dylan7474/SleepRadioPi-OS/hardware/case/stl/tabs.stl

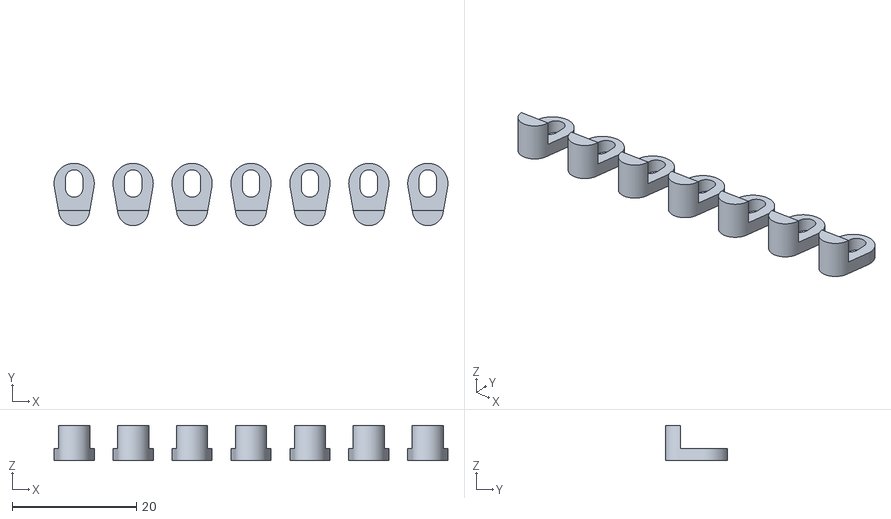
[picture p20: CAD file, 2026-09-29]
hardware/case/stl/tabs.stl
63.5 x 10.0 x 5.70
