dylan7474/SleepRadioPi-OS/hardware/case/stl/top_test.stl

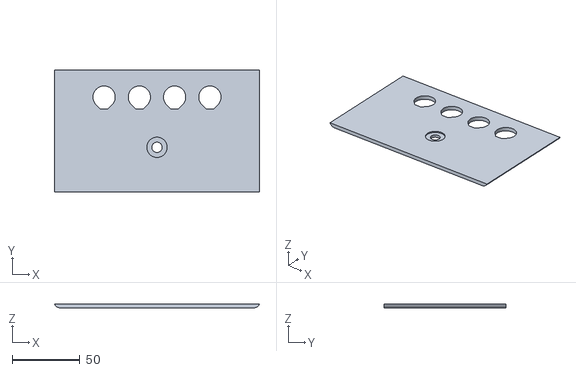
[picture p21: CAD file, 2026-09-29]
hardware/case/stl/top_test.stl
151.2 x 90.0 x 3.01
