dylan7474/SleepRadioPi-OS/hardware/case/stl/tube_buttons.stl

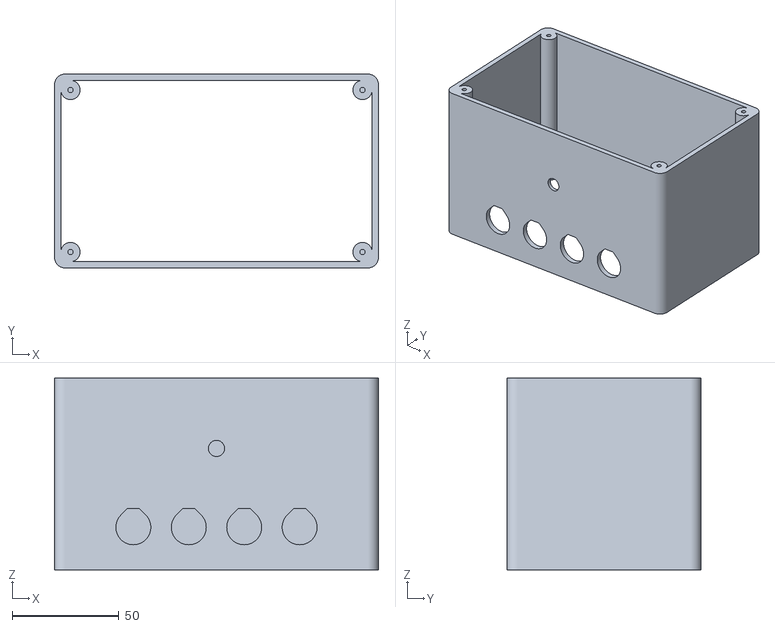
[picture p22: CAD file, 2026-09-29]
hardware/case/stl/tube_buttons.stl
152.0 x 91.0 x 90.0
