dylan7474/SleepRadioPi-OS/hardware/case/stl/strap_loops.stl

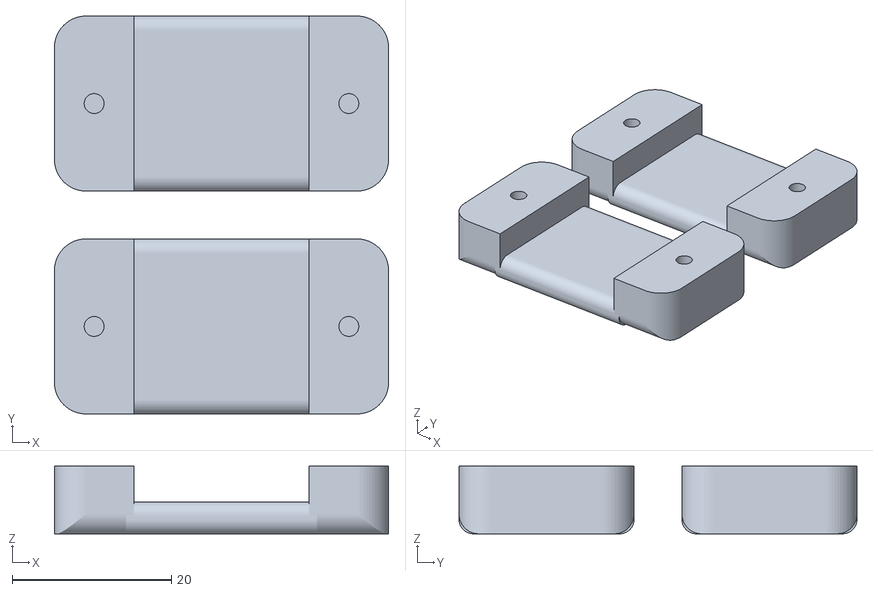
[picture p23: CAD file, 2026-09-27]
hardware/case/stl/strap_loops.stl
42.0 x 50.0 x 8.50
