dylan7474/SleepRadioPi-OS/hardware/case/stl/strap_guide.stl

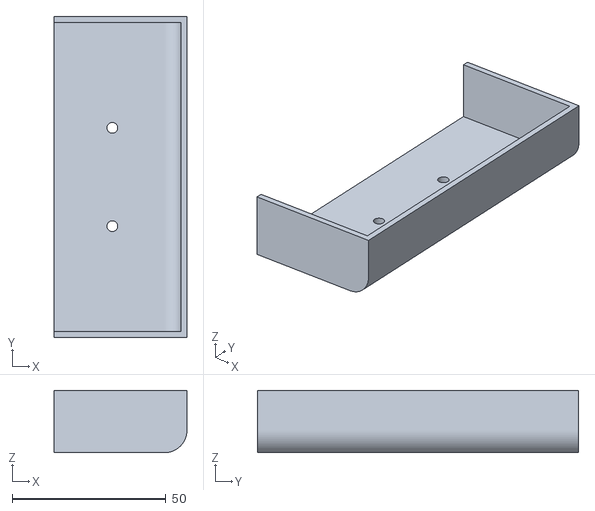
[picture p24: CAD file, 2026-09-27]
hardware/case/stl/strap_guide.stl
43.3 x 104.6 x 20.3
