dylan7474/SleepRadioPi-OS/hardware/case/stl/tube_handle.stl

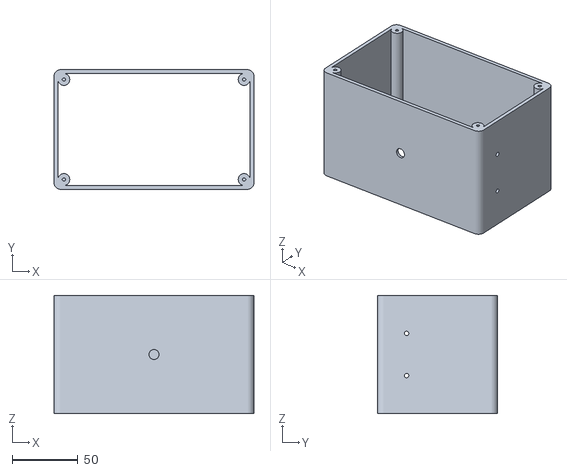
[picture p25: CAD file, 2026-09-27]
hardware/case/stl/tube_handle.stl
152.0 x 91.0 x 90.0
