dylan7474/SleepRadioPi-OS/hardware/case/stl/grommet.stl

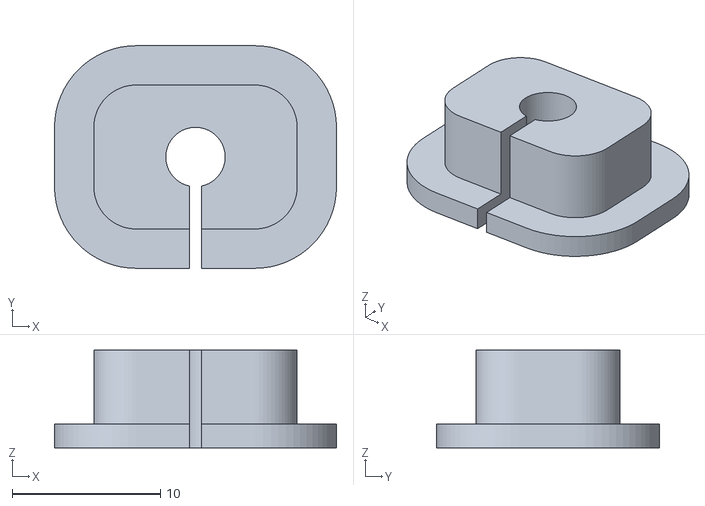
[picture p26: CAD file, 2026-09-27]
hardware/case/stl/grommet.stl
19.0 x 15.0 x 6.60
