dylan7474/SleepRadioPi-OS/hardware/case/stl/tube_ring.stl

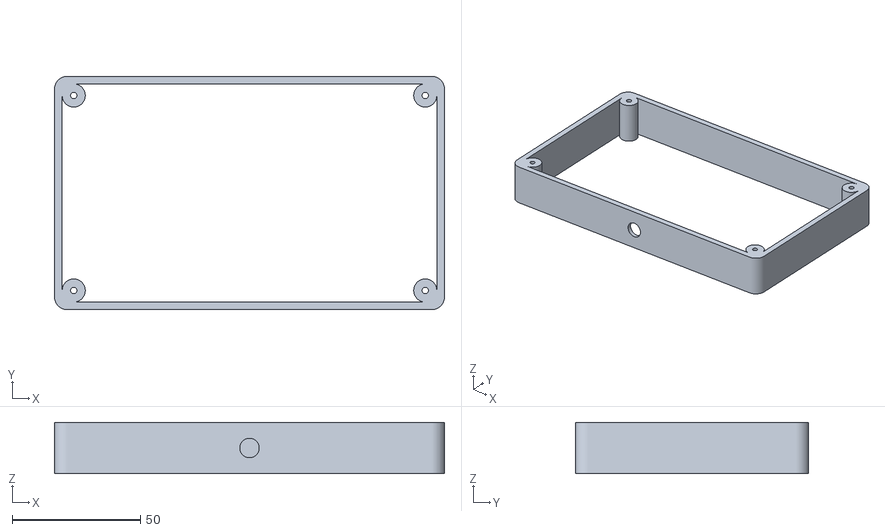
[picture p27: CAD file, 2026-09-26]
hardware/case/stl/tube_ring.stl
152.0 x 91.0 x 20.0
