dylan7474/SleepRadioPi-OS/hardware/case/sleepradiopi_box.scad

// SleepRadioPi box: a 3D-printable stereo radio cabinet for two small round
// speakers (Gikfun EK1794, 40 mm, no screw holes), a Raspberry Pi Zero 2 W +
// HiFiBerry MiniAmp, a DS3231 RTC and an EC11 rotary encoder in the top.
// No display.
//
// Printed parts that screw together:
//   tube  - top, bottom and sides in one piece, open front and back
//   front - baffle with two grilles; each speaker drops into a locating collar
//           behind its grille and is held by hot glue or three clamp tabs
//   rear  - back panel; the Pi, amp and RTC mount on its inside face, so the
//           whole electronics tray comes out with the panel
//   knob  - for the encoder's 6 mm D-shaft
//   tabs  - speaker clamp tabs (6 + 1 spare)
//   tube_ring - a 20 mm slice of the tube (same section, corner bosses and
//           knob hole) to test the panels and encoder before the full tube
//   grommet - closes the power cable slot round the cable (for the bass port)
//   strap_loops - two loops for a leather carry strap, screwed to the sides
//           from inside; strap_guide - a drill guide that clips over the box
//           to put the loops' screw holes in a tube printed without them
//   top_test - just the top wall of a -D buttons=true tube (the button and
//           knob holes), printed flat in ~40 min, to try the buttons first
//
// Render a part:
//   openscad --backend=manifold -D 'part="tube"' -o tube.stl sleepradiopi_box.scad
// part = "tube" | "tube_ring" | "front" | "rear" | "knob" | "tabs" | "grommet" | "front_plate" |
//        "strap_loops" | "strap_guide" | "top_test" |
//        "front_plate_noknob" |
//        "assembly" | "exploded" | "rear_inside" | "front_inside" | "check" | "check_pull"
//
// Coordinate frame: x across the box (0 = centre, +x = right seen from the
// front), y front to back (y = 0 is the front face), z up (0 = underside).
// Everything is in millimetres.

part = "assembly";

// A script font for the lettering, in fonts/ (SIL Open Font Licence, fonts/OFL-Lobster.txt):
// logo_font = "Lobster", with logo_fit = "together" (the Roberts Radio front)
use <fonts/Lobster-Regular.ttf>

// Draft: thin, fast fit-test panels (1.2 mm plate, open grille holes, no
// countersinks). Only for the front/rear/draft_plate parts -- never the tube.
draft = false;

// Lettering engraved into the front face between the speakers. Engraved, not
// raised: the front prints face down, and raised letters would need the whole
// panel on supports. Try -D front_logo=true with part="front" / "front_plate".
front_logo    = false;
logo_lines    = ["SLEEP", "RADIO"];
logo_font     = "Liberation Sans:style=Bold";
logo_w        = 36;      // every line is stretched to this width
logo_gap      = 4;       // between lines
logo_depth    = 0.8;     // 4 layers at 0.2 mm
logo_fit      = "stretch"; // "stretch": every line to logo_w (block capitals); "together": the lines
                         // scaled as one so the widest is logo_w, keeping the letters' shape (a script)

/* ---------- Speakers (CHECK WITH CALIPERS) ---------- */
spk_d        = 40;      // rim diameter (measured: 40 mm)
spk_rim_t    = 2.7;     // thickness of the flat front rim/flange (measured 2026-09-29)
spk_depth    = 22;      // front of the rim to the back of the magnet (UNVERIFIED)
spk_grille_d = 34;      // grille opening, a bit less than the rim so the rim seals
spk_fit      = 0.6;     // collar clearance on the diameter
collar_t     = 1.6;
clamp        = true;    // screw bosses for the clamp tabs (hot glue works without)
clamp_angles = [90, 210, 330];
clamp_r      = spk_d / 2 + collar_t + 3.2;  // boss centre radius
clamp_boss_d = 6.5;
clamp_boss_h = 6;       // boss height above the panel's inside face (screw grip)
clamp_pilot  = 2.1;     // M2.5 self-tapping (the M2.5 x 6 screws from the Pi kit)
tab_t        = 2;

/* ---------- Pi Zero 2 W + MiniAmp (datasheet values, as in the old case) ---------- */
pcb_l      = 65;
pcb_w      = 30;
pcb_t      = 1.6;
hole_in    = 3.5;
port_otg_u = 41.4;       // port centres along the long edge, from the SD end
port_pwr_u = 54;
amp_gap    = 12;         // Pi to amp, on the header
term_u0    = 23.9;       // MiniAmp speaker terminal, along the port edge
term_u1    = 44.4;
term_h     = 10;

/* ---------- Box ---------- */
inner_w     = 146;
inner_h     = 85;
ring_len    = 20;        // "tube_ring": a short slice of the tube for a fit test
tube_len    = part == "tube_ring" ? ring_len : 90;  // inside depth, front panel to rear panel
wall        = 3;
panel_t     = draft ? 1.2 : 5;
grille_t    = draft ? panel_t : 2.4;  // grille thickness; the rest is a recess for the cone
spk_x       = 45;        // speaker centres at +-spk_x
corner_r    = 5;

boss_r      = 4.5;       // screw bosses in the tube corners, for the panels
boss_off    = 4.5;       // boss centre from the inner walls
pilot_d     = 2.5;       // M3 self-tapping screws into the bosses
pilot_len   = 16;
panel_screw_d = 3.4;
panel_csk_d   = 6.6;

lip_t       = 1.6;       // locating lip on each panel, fits inside the tube
lip_h       = 3;
lip_clr     = 0.3;

hex_flat    = 3.2;       // grille: hexagonal holes, flat to flat
hex_web     = 1.2;
grille_style = "hex";    // "hex" or "sunburst" (art deco: a fan rising from the bottom)
sun_rays    = 9;         // sunburst: rays from the half-sun at the bottom of the grille
sun_spread  = 80;        // ...fanned out to +-this many degrees from vertical
sun_hub_r   = 8;         // the half-sun
sun_arc_r   = 20;        // arc across the rays; above it an extra ray between each pair
sun_rib_w   = 1.6;       // rays and arc (4 perimeters at 0.4 mm)

/* ---------- Rear panel electronics ---------- */
pi_dx       = 0;         // Pi position: offset from the centre line
post_h      = 7;         // room under the Pi for header stubs + encoder wires
post_d      = 6;         // tip, under the Pi
post_d2     = 7.6;       // below the tip
// The Pi: four M2.5 self-tappers down through its corner holes into solid
// posts (the heads sit on the Pi). The back of the panel stays plain. The
// amp sits on the Pi's header; no standoffs.
pi_tap_d      = 2.2;     // pilot for an M2.5 self-tapper (prints ~2.0; tested)

cable_dx    = 32;        // power cable slot: this far out from the Pi's port edge
cable_w     = 14;
cable_h     = 10;

// Bass port (-D rear_port=true). The box is ~0.95 L inside (both speakers
// share it); a 20 mm port 22 mm long (the panel + a tube inside) tunes it to
// ~160 Hz, just below where 40 mm speakers give up. The cable slot is a vent
// too (~160 Hz on its own), so close it with the grommet when the port is on,
// and set the radio's low cut (speaker_highpass_hz) to ~140 Hz so the bass EQ
// doesn't push the speakers below the port's note.
rear_port   = false;
port_d      = 20;
port_len    = 22;        // outside face to the tube's inner end
port_wall   = 1.6;
port_flare  = 3;         // 45-degree flare at both ends: quieter, no supports needed
port_pos    = [47, 30];  // (x, z): low down on the side away from the RTC
box_net_l   = 0.95;      // inside volume less the speakers, Pi, bosses (estimated)

grommet_clr     = 0.15;  // plug vs the slot, each side
grommet_cable_d = 4;     // micro-USB cable (CHECK WITH CALIPERS)
grommet_slit    = 0.8;   // so it springs round the cable
grommet_flange  = 2.5;   // outside lip, all round
grommet_flange_t = 1.6;

rtc         = true;      // ZS-042 DS3231: a locating rim, fix with foam tape
rtc_w       = 22.5;
rtc_l       = 38.5;
rtc_gap     = 17;        // from the Pi's GPIO edge to the RTC rim

/* ---------- Encoder + knob ---------- */
enc_hole_d  = 7.6;       // EC11 M7 bushing (a little over, for the sideways print)
enc_teardrop = false;    // true = pointed top, for printers that sag on round holes
enc_pocket_d = 15;       // thin the top wall around it so the nut gets thread
enc_pocket  = 1;
knob_d      = 30;
knob_h      = 20;
knob_style  = "plain";   // "plain" (pointer groove) or "sunburst" (the grille's fan
                         // engraved in the top; it rises towards where the groove points)
knob_sun_d  = 26;
knob_sun_rays = 7;
knob_sun_rib_w = 1.4;
knob_engrave = 0.8;
shaft_d     = 6.15;
shaft_flat  = 4.65;
shaft_len   = 16.5;      // bore depth: a 20 mm EC11 shaft stands ~18 mm above the
                         // case (2 mm wall at the pocket), so the knob clears it by ~1.5 mm
nut_recess_d = 12;       // under the knob, round the encoder's M7 nut + washer
nut_recess_h = 3;

/* ---------- Preset buttons ---------- */
// Four chunky momentary panel buttons (16 mm stainless, screw terminals) in a
// row across the top, near the front, with the knob on its own further back:
// the channels and the volume in separate places, which is easier to follow
// (the radio is for an elderly listener). Wiring: hardware/wiring.
// -D buttons=true puts the holes in the tube and moves the knob back
// btn_knob_back mm to make room; part="top_test" is just that top, to try
// the buttons before printing a whole tube.
buttons     = false;
btn_hole_d  = 16.4;      // 16 mm thread (CHECK the buttons)
btn_x       = [-39, -13, 13, 39];   // 26 mm apart; the outer two miss the speakers' top
                                    // clamp tabs (and screws) at +-45
btn_y       = 25;        // from the front face: clear of the front panel's lip and the
                         // clamp tabs, and ~13 mm in front of the knob
btn_knob_back = 12;      // the knob moves this far back with the buttons in
btn_teardrop = true;     // the holes print sideways (the tube stands on its front end): a
                         // teardrop top, cut flat just inside the button's head, so there's
                         // no overhang to curl up and catch the nozzle (and it's hidden)
btn_head_d  = 19;        // the flat head above the top (CHECK)
btn_head_h  = 3;
btn_nut_d   = 22;        // the nut inside, across its corners (CHECK)
btn_body_d  = 18;        // below the nut: the switch body and its screw terminals (CHECK)
btn_body_h  = 30;        // top of the wall to the ends of the terminals (CHECK)

/* ---------- Carry strap ---------- */
// A leather strap over the top, through a loop on each side: the strap goes
// down behind the loop's bar, folds back up over it and is fixed to itself
// above the loop (Chicago screws or rivets). Each loop has two M3 x 10
// self-tappers from inside the box, through the side wall into its pilots.
// -D handle=true puts the holes in the tube; for a tube printed without them,
// drill them through strap_guide.
handle      = false;
strap_w     = 20;        // leather strap (CHECK: the channel is 2 mm wider)
strap_t     = 4;         // ...and its thickness (the channel is 0.5 mm deeper)
loop_side   = 10;        // screw lugs either side of the strap channel
loop_h      = 22;        // top to bottom
loop_bar    = 4;         // the bar the strap folds round
loop_top    = 11;        // below the top of the box (clear of the corner bosses inside)
loop_pilot  = 2.5;       // M3 self-tapping
loop_skin   = 1.2;       // plastic left over the end of each pilot
loop_hole_d = 3.4;       // through the side wall
guide_hole_d = 3.5;      // the drill guide's holes: drill 3.5 mm
guide_t     = 2;
guide_clr   = 0.3;

$fn = 64;

/* ---------- Derived ---------- */
W  = inner_w + 2 * wall;
H  = inner_h + 2 * wall;
D  = tube_len + 2 * panel_t;
ti = panel_t;                 // tube front end (inside face of the front panel)
to = panel_t + tube_len;      // tube rear end (inside face of the rear panel)

spk_z   = H / 2;
spk_pos = [[-spk_x, spk_z], [spk_x, spk_z]];
collar_h = spk_rim_t - 0.4;   // a little under the rim, so the tabs clamp the speaker
function clamp_pts(p) = [for (a = clamp_angles) p + clamp_r * [cos(a), sin(a)]];

bx = inner_w / 2 - boss_off;
bz0 = wall + boss_off;
bz1 = H - wall - boss_off;
bosses = [[-bx, bz0, -1, -1], [bx, bz0, 1, -1], [-bx, bz1, -1, 1], [bx, bz1, 1, 1]];

enc_y = ti + tube_len / 2 + (buttons ? btn_knob_back : 0);

loop_cw = strap_w + 2;                       // strap channel width
loop_gap = strap_t + 0.5;                    // channel depth (the strap runs between the wall and the bar)
loop_t = loop_gap + loop_bar;                // how far a loop stands out from the side
loop_l = loop_cw + 2 * loop_side;
loop_dy = loop_cw / 2 + loop_side / 2;       // screws either side of the middle
loop_y = D / 2;                              // centred front to back (the balance point)
loop_z = H - loop_top - loop_h / 2;
loop_screws = [for (sx = [-1, 1]) for (dy = [-loop_dy, loop_dy]) [sx, loop_y + dy]];

// Pi on the rear panel, long side vertical, SD end down, parts facing forward,
// ports on the +x edge.
pi_x0   = pi_dx - pcb_w / 2;
pi_z0   = H / 2 - pcb_l / 2;
pi_y    = to - post_h;               // Pi underside
pi_top  = pi_y - pcb_t;              // component side (faces the front)
amp_y   = pi_top - amp_gap;          // amp underside
amp_top = amp_y - pcb_t;
port_x  = pi_x0 + pcb_w;             // port edge
function pi_pt(u, v) = [port_x - v, pi_z0 + u];  // board coords -> (x, z)
pi_holes = [for (u = [hole_in, pcb_l - hole_in]) for (v = [hole_in, pcb_w - hole_in]) pi_pt(u, v)];
cable_pos = [port_x + cable_dx, pi_z0 + port_pwr_u];
rtc_pos   = [pi_x0 - rtc_gap - rtc_w / 2, H / 2];

if (rear_port) {
    a = PI * port_d * port_d / 4;
    leff = port_len + 0.85 * port_d;   // end correction 1.7 r
    echo(str("Bass port: ", port_d, " mm x ", port_len, " mm -> tuned to about ",
             round(343000 / (2 * PI) * sqrt(a / (box_net_l * 1e6 * leff))), " Hz"));
}

echo(str("Outer size: ", W, " x ", D, " x ", H, " mm (w x d x h); inside ",
         inner_w, " x ", tube_len, " x ", inner_h, " = ",
         round(inner_w * tube_len * inner_h / 1e4) / 100, " L"));

// The speaker mounts must stay clear of the lip and the corner bosses.
lip_in = [inner_w / 2 - lip_clr - lip_t, inner_h / 2 - lip_clr - lip_t];
for (p = spk_pos) for (c = concat([p + [sign(p[0]) * (spk_d / 2 + collar_t), 0]],
                                  clamp ? clamp_pts(p) : [])) {
    r = norm(c - p) > spk_d / 2 + collar_t + 0.1 ? clamp_boss_d / 2 : 0;
    assert(abs(c[0]) + r < lip_in[0] - 0.5 && abs(c[1] - H / 2) + r < lip_in[1] - 0.5,
           "A speaker mount hits the panel lip: move spk_x or the clamp angles");
    for (b = bosses) assert(norm(c - [b[0], b[1]]) > r + boss_r + 1, "A speaker mount hits a corner boss");
}

/* ---------- Helpers ---------- */
module rrect(x0, z0, x1, z1, r) {
    r = max(r, 0.01);
    hull() for (x = [x0 + r, x1 - r], z = [z0 + r, z1 - r]) translate([x, z]) circle(r = r);
}
// Extrude an (x, z) profile along y from y0 to y1.
module yext(y0, y1) translate([0, y1, 0]) rotate([90, 0, 0]) linear_extrude(y1 - y0) children();
// A cylinder along y.
module ycyl(x, z, y0, y1, d, d2 = undef)
    translate([x, y0, z]) rotate([-90, 0, 0]) cylinder(d1 = d, d2 = is_undef(d2) ? d : d2, h = y1 - y0);

module outer2d() rrect(-W / 2, 0, W / 2, H, corner_r);
module inner2d(inset = 0)
    rrect(-inner_w / 2 + inset, wall + inset, inner_w / 2 - inset, H - wall - inset,
          max(corner_r - wall - inset, 0.5));

// Corner boss profile: a circle hulled into the corner.
module boss2d(b, grow = 0) hull() {
    translate([b[0], b[1]]) circle(r = boss_r + grow);
    translate([b[0] + b[2] * (boss_off + grow), b[1] + b[3] * (boss_off + grow)]) square(0.02, center = true);
    translate([b[0] + b[2] * (boss_off + grow), b[1] - b[3] * grow]) square(0.02, center = true);
    translate([b[0] - b[2] * grow, b[1] + b[3] * (boss_off + grow)]) square(0.02, center = true);
}

/* ---------- Tube ---------- */
module teardrop2d(d) hull() {   // point towards +y (up while the tube prints)
    circle(d = d);
    translate([0, d / 2 * sqrt(2)]) square(0.02, center = true);
}

module enc2d(d) if (enc_teardrop) teardrop2d(d); else circle(d = d);
module btn2d(d) if (btn_teardrop) intersection() {
    teardrop2d(d);
    translate([-d, -d]) square([2 * d, d + min(d / 2 * sqrt(2), btn_head_d / 2 - 0.75)]);
} else circle(d = d);

module tube() {
    difference() {
        union() {
            yext(ti, to) difference() { outer2d(); inner2d(); }
            for (b = bosses) yext(ti, to) boss2d(b);
        }
        for (b = bosses) {
            ycyl(b[0], b[1], ti - 1, ti + pilot_len, pilot_d);
            ycyl(b[0], b[1], to - pilot_len, to + 1, pilot_d);
        }
        if (handle) strap_holes(loop_hole_d);
        if (buttons) for (x = btn_x)
            translate([x, btn_y, H - wall - 1]) linear_extrude(wall + 2) btn2d(btn_hole_d);
        // Encoder hole in the top, with a thinner patch of wall around it.
        translate([0, enc_y, H - wall - 1]) linear_extrude(wall + 2) enc2d(enc_hole_d);
        translate([0, enc_y, H - wall - 1]) linear_extrude(1 + enc_pocket) enc2d(enc_pocket_d);
    }
}

/* ---------- Panels (shared) ---------- */
// Built with the outside face at y = 0 and the inside face at y = panel_t,
// the lip sticking out to y = panel_t + lip_h.
module panel_blank() {
    yext(0, panel_t) outer2d();
    yext(panel_t - 0.01, panel_t + lip_h) difference() {
        inner2d(lip_clr);
        inner2d(lip_clr + lip_t);
        for (b = bosses) boss2d(b, 0.6);
    }
}
module panel_screw_holes() for (b = bosses) {
    ycyl(b[0], b[1], -1, panel_t + 1, panel_screw_d);
    if (!draft) ycyl(b[0], b[1], -0.01, (panel_csk_d - panel_screw_d) / 2, panel_csk_d, panel_screw_d);
}

/* ---------- Front panel ---------- */
hex_pitch = hex_flat + hex_web;
module grille2d(style = grille_style) {
    if (style == "sunburst") sunburst2d(); else hex2d();
}
// Art deco sunburst, 1930s radio style: rays fan up from a half-sun at the
// bottom of the grille, with an arc across them and extra rays above the arc
// so the top slots stay narrow. The open slots are what's left of the circle.
// d and rays default to the speaker grille; the hub and arc scale with d.
module sunburst2d(d = spk_grille_d, rays = sun_rays, rib_w = sun_rib_w) {
    k = d / spk_grille_d;
    step = 2 * sun_spread / (rays - 1);
    module ray(a, r0) rotate(90 + a) translate([r0, -rib_w / 2]) square([d * 2, rib_w]);
    translate([0, -d / 2]) difference() {
        translate([0, d / 2]) circle(d = d);
        circle(r = sun_hub_r * k);
        for (i = [0 : rays - 1]) ray(-sun_spread + i * step, 0);
        for (i = [0 : rays - 2]) ray(-sun_spread + (i + 0.5) * step, sun_arc_r * k);
        difference() { circle(r = sun_arc_r * k + rib_w / 2); circle(r = sun_arc_r * k - rib_w / 2); }
    }
}
module hex2d() intersection() {
    circle(d = spk_grille_d);
    n = ceil(spk_grille_d / hex_pitch);
    for (j = [-n : n]) for (i = [-n : n])
        translate([(i + (j % 2) / 2) * hex_pitch, j * hex_pitch * sqrt(3) / 2])
            rotate(30) circle(d = hex_flat / cos(30), $fn = 6);
}

module front(logo = front_logo, grille = grille_style) {
    difference() {
        union() {
            panel_blank();
            for (p = spk_pos) translate([p[0], 0, p[1]]) {
                // Locating collar around the speaker rim
                yext(panel_t - 0.01, panel_t + collar_h) difference() {
                    circle(d = spk_d + spk_fit + 2 * collar_t);
                    circle(d = spk_d + spk_fit);
                }
            }
            if (clamp) for (p = spk_pos) for (c = clamp_pts(p))
                ycyl(c[0], c[1], panel_t - 0.01, panel_t + clamp_boss_h, clamp_boss_d);
        }
        panel_screw_holes();
        for (p = spk_pos) translate([p[0], 0, p[1]]) {
            yext(-1, panel_t + 1) if (draft) circle(d = spk_grille_d); else grille2d(grille);
            yext(grille_t, panel_t + 1) circle(d = spk_grille_d);  // cone clearance
        }
        if (clamp) for (p = spk_pos) for (c = clamp_pts(p))
            ycyl(c[0], c[1], draft ? -1 : 1.2, panel_t + clamp_boss_h + 1, clamp_pilot);
        if (logo && !draft) yext(-1, logo_depth) logo2d();
    }
}


// The lettering, centred between the speakers: each line the same width, or (logo_fit
// "together") all scaled as one, keeping the font's shape
module logo2d() {
    if (logo_fit == "together") logo_together2d(); else logo_stretched2d();
}
module logo_together2d() {
    n = len(logo_lines);
    translate([0, spk_z]) resize([logo_w, 0], auto = true)
        for (i = [0 : n - 1])
            translate([0, ((n - 1) / 2 - i) * 13])
                text(logo_lines[i], size = 10, font = logo_font, halign = "center", valign = "center");
}
module logo_stretched2d() {
    n = len(logo_lines);
    line_h = logo_line_h();
    total = n * line_h + (n - 1) * logo_gap;
    for (i = [0 : n - 1])
        translate([0, spk_z + total / 2 - line_h / 2 - i * (line_h + logo_gap)])
            resize([logo_w, line_h])
                text(logo_lines[i], size = 10, font = logo_font, halign = "center", valign = "center");
}
// Cap height once a line is stretched to logo_w (Liberation Sans Bold caps
// are about 0.72 x size tall and ~0.72 x size wide per letter)
function logo_line_h() = logo_w / max([for (l = logo_lines) len(l)]) * 1.0;

/* ---------- Speaker clamp tab ---------- */
// Stepped tab: the plate sits on the tall boss with the screw in the slot, and
// a foot under the rounded nose reaches down and presses on the rim. The foot
// stops short of the boss, even with the tab pulled back along its slot.
// Local z = 0 is the foot's underside; the plate is on top.
tab_len  = clamp_r - spk_d / 2 + 2;    // reaches 2 mm over the rim
tab_drop = clamp_boss_h - collar_h;    // foot height: rim + 0.4 mm press
tab_foot_x = -(clamp_boss_d / 2 + 0.8 + 0.3);
module tab2d() difference() {
    hull() { circle(d = clamp_boss_d); translate([-tab_len + 2.5, 0]) circle(d = 5); }
    hull() for (dx = [-0.8, 0.8]) translate([dx, 0]) circle(d = 2.8);  // slot for the M2.5 screw
}
module tab() {
    translate([0, 0, tab_drop]) linear_extrude(tab_t) tab2d();
    linear_extrude(tab_drop + 0.01) intersection() {
        tab2d();
        translate([tab_foot_x - 20, -10]) square([20, 20]);
    }
}
module tab_print() translate([0, 0, tab_drop + tab_t]) mirror([0, 0, 1]) tab();  // plate down, foot up

/* ---------- Rear panel ---------- */
// Built in place (outside face at y = D), so the Pi coordinates line up.
module rear() {
    difference() {
        union() {
            translate([0, D, 0]) mirror([0, 1, 0]) panel_blank();
            // Solid posts: a narrow tip next to the board (clear of the header
            // pins), thicker below.
            for (h = pi_holes) {
                ycyl(h[0], h[1], pi_y, pi_y + 3, post_d);
                ycyl(h[0], h[1], pi_y + 3 - 0.01, to + 0.01, post_d2);
            }
            if (rtc) yext(to - 3, to + 0.01) translate(rtc_pos) difference() {
                square([rtc_w + 2.4, rtc_l + 2.4], center = true);
                square([rtc_w, rtc_l], center = true);
                square([rtc_w - 6, rtc_l + 4], center = true);  // gaps for the header wires
            }
            if (rear_port) port_tube();
        }
        if (rear_port) port_bore();
        translate([0, D, 0]) mirror([0, 1, 0]) panel_screw_holes();
        // Self-tapper pilots, stopping 1.2 mm short of the outside face
        for (h = pi_holes) ycyl(h[0], h[1], pi_y - 1, D - 1.2, pi_tap_d);
        // Power cable slot (the micro-USB plug threads through it) + zip-tie slots
        yext(to - 1, D + 1) {
            translate(cable_pos) rrect(-cable_w / 2, -cable_h / 2, cable_w / 2, cable_h / 2, 3);
            for (dz = [-8, 8]) translate(cable_pos + [cable_w / 2 + 6, dz])
                square([5, 3], center = true);
        }
    }
}

// Bass port: a tube on the inside face, flared at both ends.
port_tip = D - port_len;                 // y of the tube's inner end
module port_tube() {
    od = port_d + 2 * port_wall;
    ycyl(port_pos[0], port_pos[1], port_tip + port_flare, to + 0.01, od);
    ycyl(port_pos[0], port_pos[1], port_tip, port_tip + port_flare + 0.01, od + 2 * port_flare, od);
}
module port_bore() {
    ycyl(port_pos[0], port_pos[1], port_tip - 1, D + 1, port_d);
    ycyl(port_pos[0], port_pos[1], port_tip - 0.01, port_tip + port_flare, port_d + 2 * port_flare, port_d);
    ycyl(port_pos[0], port_pos[1], D - port_flare, D + 0.01, port_d, port_d + 2 * port_flare);
}

/* ---------- Grommet (print flange down) ---------- */
// Fills the power cable slot round the cable once the plug is through. Open
// the slit, clip it round the cable, press it into the slot from outside.
module grommet() {
    module slot2d(grow) rrect(-cable_w / 2 - grow, -cable_h / 2 - grow,
                              cable_w / 2 + grow, cable_h / 2 + grow, 3 + max(grow, -2.9));
    difference() {
        union() {
            linear_extrude(grommet_flange_t) slot2d(grommet_flange);
            linear_extrude(grommet_flange_t + panel_t) slot2d(-grommet_clr);
        }
        translate([0, 0, -1]) {
            cylinder(d = grommet_cable_d, h = panel_t + grommet_flange_t + 2);
            translate([-grommet_slit / 2, -cable_h, 0]) cube([grommet_slit, cable_h, panel_t + grommet_flange_t + 2]);
        }
    }
}
module grommet_in_place() translate([cable_pos[0], D + grommet_flange_t, cable_pos[1]])
    rotate([90, 0, 0]) grommet();

/* ---------- Knob (print top face down) ---------- */
/* ---------- Carry strap loops ---------- */
// Extrude a (y, z) profile along x from x0 to x1.
module xext(x0, x1) translate([x0, 0, 0]) rotate([90, 0, 90]) linear_extrude(x1 - x0) children();

// One loop, built with x along the strap's width, y up and z out from the
// side wall (z = 0 against the wall).
module strap_loop() {
    difference() {
        intersection() {
            translate([0, 0, -1]) linear_extrude(loop_t + 2)
                rrect(-loop_l / 2, -loop_h / 2, loop_l / 2, loop_h / 2, 4);
            union() {
                // the screw lugs: rounded on the outside
                for (sx = [-1, 1]) xext(sx > 0 ? loop_cw / 2 : -loop_l / 2 - 1,
                                        sx > 0 ? loop_l / 2 + 1 : -loop_cw / 2) hull() {
                    translate([-loop_h / 2, 0]) square([loop_h, 0.01]);
                    for (y = [-1, 1]) translate([y * (loop_h / 2 - 2.5), loop_t - 2.5]) circle(r = 2.5);
                }
                // the bar, rounded all round so the leather folds over it easily
                xext(-loop_cw / 2 - 1, loop_cw / 2 + 1) rrect(-loop_h / 2, loop_gap, loop_h / 2, loop_t, 1.8);
            }
        }
        for (sx = [-1, 1]) translate([sx * loop_dy, 0, -1]) cylinder(d = loop_pilot, h = 1 + loop_t - loop_skin);
    }
}
// The loops on the box: the right one, and the left one mirrored.
module strap_loops_placed() for (sx = [-1, 1]) mirror([sx < 0 ? 1 : 0, 0, 0])
    multmatrix([[0, 0, 1, W / 2], [1, 0, 0, loop_y], [0, 1, 0, loop_z], [0, 0, 0, 1]]) strap_loop();
// The screw holes through the side walls (also the screws, for the checks).
module strap_holes(d, len = wall + 2) for (sc = loop_screws)
    translate([sc[0] * (W / 2 - wall - 1 + len / 2), sc[1], loop_z]) rotate([0, 90, 0]) cylinder(d = d, h = len, center = true);
// M3 x 10: a pan head inside the box, 3 mm of wall, 7 mm into the loop.
module strap_screws() {
    strap_holes(3, 10 + 2);
    for (sc = loop_screws) translate([sc[0] * (W / 2 - wall - 1.2), sc[1], loop_z]) rotate([0, 90, 0])
        cylinder(d = 5.6, h = 2.4, center = true);
}
// Drill guide for a tube without the holes: clips over the top corner of the
// assembled box, between stops on the front and back panels' faces, and
// turns round end to end for the other side. Drill 3.5 mm through its holes.
module strap_guide() {
    win = [W / 2 - 18, loop_z - loop_h / 2 - 8];
    module window() translate(win) square([40, 60]);
    difference() {
        union() {
            yext(-guide_clr, D + guide_clr) intersection() {
                difference() { offset(r = guide_clr + guide_t) outer2d(); offset(r = guide_clr) outer2d(); }
                window();
            }
            for (y = [-guide_clr - guide_t, D + guide_clr]) yext(y, y + guide_t)
                intersection() { offset(r = guide_clr + guide_t) outer2d(); window(); }
        }
        for (sc = loop_screws) if (sc[0] > 0)
            translate([W / 2 - 1, sc[1], loop_z]) rotate([0, 90, 0]) cylinder(d = guide_hole_d, h = 10);
    }
}

// Just the top wall of the tube (with the buttons' and the knob's holes),
// printed flat, outside face down: try the buttons, nuts and spacing first.
module top_test() intersection() {
    tube();
    translate([-W / 2 - 1, ti, H - wall - 0.01]) cube([W + 2, tube_len, wall + 1]);
}

module knob(style = knob_style) {
    difference() {
        union() {
            cylinder(d = knob_d - 1.2, h = knob_h);
            for (a = [0 : 360 / 36 : 359]) rotate([0, 0, a])
                translate([knob_d / 2 - 1.1, 0, 0]) cylinder(d = 1.8, h = knob_h, $fn = 12);
        }
        translate([0, 0, -0.01]) intersection() {
            cylinder(d = shaft_d, h = shaft_len);
            translate([-shaft_d / 2, -shaft_d / 2, 0]) cube([shaft_flat, shaft_d, shaft_len]);
        }
        translate([0, 0, -0.01]) cylinder(d = nut_recess_d, h = nut_recess_h);
        // Hollow skirt around the shaft so the knob clears the nut
        translate([0, 0, -0.01]) difference() {
            cylinder(d = knob_d - 6, h = 4);
            cylinder(d = shaft_d + 4, h = 4);
        }
        if (style == "sunburst")
            translate([0, 0, knob_h - knob_engrave]) linear_extrude(knob_engrave + 0.01)
                rotate(-90) sunburst2d(knob_sun_d, knob_sun_rays, knob_sun_rib_w);
        else
            translate([0, -0.7, knob_h - 1]) cube([knob_d / 2 - 3, 1.4, 1.2]);
    }
}

/* ---------- Part models for previews and checks ---------- */
module speaker_model(p) color("dimgray") translate([p[0], 0, p[1]]) {
    ycyl(0, 0, ti, ti + spk_rim_t, spk_d);
    ycyl(0, 0, ti + spk_rim_t, ti + spk_depth - 8, spk_d - 6, 20);   // basket
    ycyl(0, 0, ti + spk_depth - 8, ti + spk_depth, 24);
    // Solder tabs, placed between two clamp bosses
    rotate([0, -30, 0]) translate([spk_d / 2 - 5, ti + spk_rim_t + 1, -2]) cube([6, 4, 4]);
}
module tabs_in_place() color("orange") for (p = spk_pos) for (a = clamp_angles)
    translate([p[0], 0, p[1]]) rotate([0, -a, 0]) translate([clamp_r, ti + spk_rim_t, 0])
        rotate([-90, 0, 0]) tab();

module pi_stack_model() {
    module board(y, c) color(c) yext(y - pcb_t, y) translate([pi_x0, pi_z0]) square([pcb_w, pcb_l]);
    board(pi_y, "green");
    board(amp_y, "darkgreen");
    // GPIO header + socket along the far edge
    color("black") yext(amp_y, pi_top) translate([pi_x0 + 0.5, pi_z0 + 7]) square([5, 51]);
    color("black") yext(pi_y, pi_y + 3) translate([pi_x0 + 0.5, pi_z0 + 7]) square([5, 51]);  // pin stubs
    // Ports
    color("silver") for (u = [port_otg_u, port_pwr_u])
        yext(pi_top - 2.6, pi_top) translate([port_x - 5, pi_z0 + u - 4]) square([5.5, 8]);
    // Amp speaker terminal
    color("dimgray") yext(amp_top - term_h, amp_top)
        translate([port_x - 7.5, pi_z0 + term_u0]) square([7.9, term_u1 - term_u0]);
    // Micro-USB power plug + cable bend: keep-out volume
    color("white", 0.8) yext(pi_top - 8, pi_top + 1)
        translate([port_x - 0.5, pi_z0 + port_pwr_u - 5.5]) square([24, 11]);
    // RTC module (board + CR2032 holder behind it)
    if (rtc) color("steelblue") yext(to - 9, to)
        translate(rtc_pos) square([rtc_w - 0.4, rtc_l - 0.4], center = true);
}

module encoder_model() color("gray") translate([0, enc_y, 0]) {
    translate([-6.5, -6.5, H - wall - 7]) cube([13, 13, 7]);
    translate([-5, -4, H - wall - 12]) cube([10, 8, 5]);   // pins + wires
    translate([0, 0, H - wall - 7]) cylinder(d = 6, h = wall + 7 + 14);
    translate([0, 0, H - wall]) cylinder(d = 7, h = wall + 5);
}

module knob_in_place() color("orange") translate([0, enc_y, H + 2]) knob();

// The preset buttons, fitted: cap above the top, thread through it, nut and body below.
module buttons_model() color("goldenrod") for (x = btn_x) translate([x, btn_y, 0]) {
    translate([0, 0, H]) cylinder(d = btn_head_d, h = btn_head_h);
    translate([0, 0, H - wall]) cylinder(d = 11.9, h = wall);
    translate([0, 0, H - wall - 2]) cylinder(d = btn_nut_d, h = 2, $fn = 6);   // (d = across the corners)
    translate([0, 0, H - btn_body_h]) cylinder(d = btn_body_d, h = btn_body_h - wall - 2);
}

// Uncoloured versions for mockup.scad (it picks its own colours)
module knob_placed(style = knob_style) translate([0, enc_y, H + 2]) knob(style);
module speakers_placed() for (p = spk_pos) translate([p[0], 0, p[1]]) {
    ycyl(0, 0, ti, ti + spk_rim_t, spk_d);
    ycyl(0, 0, ti + spk_rim_t, ti + spk_depth - 8, spk_d - 6, 20);
}

module models() {
    for (p = spk_pos) speaker_model(p);
    pi_stack_model();
    encoder_model();
    if (buttons) buttons_model();
}

/* ---------- Print orientation ---------- */
module tube_print()  rotate([90, 0, 0]) translate([0, -ti, 0]) tube();          // front end down
module front_print() rotate([90, 0, 0]) front();                               // face down
module rear_print()  translate([0, 0, D]) rotate([-90, 0, 0]) rear();          // outside face down
module knob_print()  translate([0, 0, knob_h]) rotate([180, 0, 0]) knob();
module strap_loops_print() for (i = [0, 1]) translate([0, i * (loop_h + 6), loop_t]) mirror([0, 0, 1]) strap_loop();  // bar down
module strap_guide_print() translate([0, 0, W / 2 + guide_clr + guide_t]) rotate([0, 90, 0]) translate([0, -D / 2, 0]) strap_guide();  // side down
module top_test_print() translate([0, 0, H]) rotate([180, 0, 0]) top_test();  // outside face down
module tabs_print()  for (i = [0 : 6]) translate([i * (clamp_boss_d + 3), 0, 0]) rotate(90) tab_print();

if (part == "tube" || part == "tube_ring") tube_print();
else if (part == "front") front_print();
else if (part == "rear") rear_print();
else if (part == "knob") knob_print();
else if (part == "tabs") tabs_print();
else if (part == "grommet") grommet();
else if (part == "strap_loops") strap_loops_print();
else if (part == "strap_guide") strap_guide_print();
else if (part == "top_test") top_test_print();
else if (part == "draft_plate") {   // run with -D draft=true: both panels + tabs
    front_print();
    translate([0, 6, 0]) rear_print();
    for (i = [0 : 6]) translate([W / 2 + 12, -H / 2 - 27 + i * (clamp_boss_d + 3), 0]) tab_print();
}
else if (part == "front_plate") {   // front panel + knob + tabs on one bed
    front_print();
    translate([-W / 2 + knob_d / 2, knob_d / 2 + 6, 0]) knob_print();
    translate([-W / 2 + knob_d + 10, 12, 0]) tabs_print();
}
else if (part == "front_plate_noknob") {   // same, without the knob (print knob.scad in another colour)
    front_print();
    translate([-W / 2 + knob_d + 10, 12, 0]) tabs_print();
}
else if (part == "assembly") {
    color("burlywood") tube();
    color("tan") front();
    color("tan") rear();
    models();
    if (clamp) tabs_in_place();
    knob_in_place();
}
else if (part == "exploded") {
    color("burlywood", 0.9) tube();
    translate([0, -60, 0]) { color("tan") front(); for (p = spk_pos) speaker_model(p); if (clamp) tabs_in_place(); }
    translate([0, 90, 0]) { color("tan") rear(); pi_stack_model(); }
    encoder_model();
    knob_in_place();
}
else if (part == "rear_inside") { color("tan") rear(); pi_stack_model(); if (rear_port) color("orange") grommet_in_place(); }
else if (part == "front_inside") {
    color("tan") front();
    speaker_model(spk_pos[1]);
    if (clamp) color("orange") for (a = clamp_angles)
        translate([spk_x, 0, spk_z]) rotate([0, -a, 0]) translate([clamp_r, ti + spk_rim_t, 0]) rotate([-90, 0, 0]) tab();
}
// Interference checks: each should come out empty (touching faces show up as
// zero-volume slivers, which is fine).
else if (part == "check") {
    intersection() { tube(); union() { front(); rear(); } }
    intersection() { union() { tube(); front(); rear(); } models(); }
    intersection() { union() { for (p = spk_pos) speaker_model(p); } union() { pi_stack_model(); encoder_model(); } }
    intersection() { pi_stack_model(); encoder_model(); }
    if (buttons) {
        // the buttons: clear of the speakers, the electronics, the knob and the corner bosses
        intersection() { buttons_model(); union() { for (p = spk_pos) speaker_model(p); pi_stack_model();
                                                    encoder_model(); knob_in_place();
                                                    for (b = bosses) yext(ti, to) boss2d(b); } }
        intersection() { buttons_model(); union() { front(); rear(); } }
    }
    if (clamp) intersection() { tabs_in_place(); union() { tube(); front(); for (p = spk_pos) speaker_model(p); } }
    if (handle) {
        intersection() { strap_loops_placed(); union() { tube(); front(); rear(); } }
        // the screws inside: clear of the corner bosses, the speakers and the electronics
        intersection() { strap_screws(); union() { for (b = bosses) yext(ti, to) boss2d(b); models(); } }
    }
}
// The rear panel with everything on it slides straight out of the back.
else if (part == "check_pull")
    intersection() {
        hull() for (dy = [0, tube_len + 20]) translate([0, dy, 0]) pi_stack_model();
        union() { tube(); encoder_model(); for (p = spk_pos) speaker_model(p); }
    }
